BrendonBuilds/mod0/CAD/Extruders/E3DRevoHemeraXS_FLYRRF36_CAN/README.md

# E3DRevoHemeraXS_FLYRRF36_CAN_magZ-v1

- *This project is a work in progress*
- *Expect files to change*

## BOM

- Magnetic Connectors - https://www.adafruit.com/product/5360
- Limit Switch - https://www.digikey.com/en/products/detail/omron-electronics-inc-emc-div/D2GW-A02D/15963578

## Reference Models

- FLY RRF 36 Toolboards
  - https://teamgloomy.github.io/fly_rrf_36_general.html
- E3D Hemera XS:
  - https://e3d-online.com/products/revo-hemera-xs
  - https://cdn.shopify.com/s/files/1/0259/1948/8059/files/Hemera_XS_Reference_CAD.STEP?v=1693395523

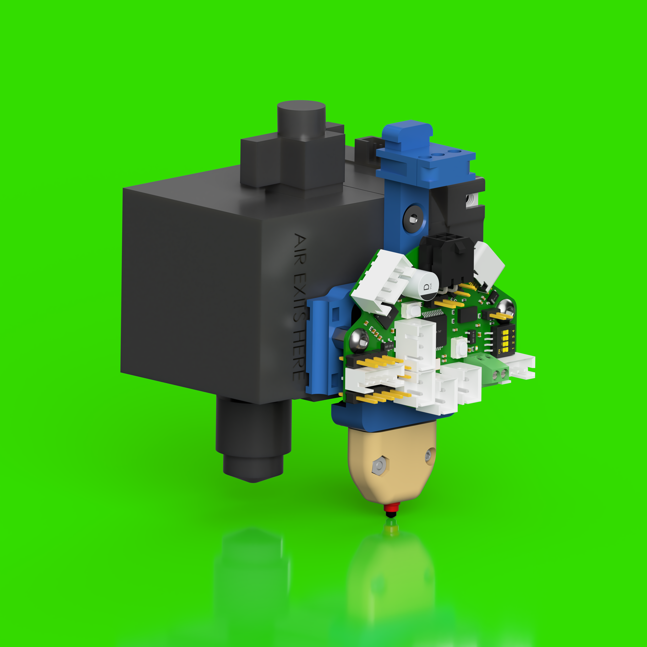
[picture p19: CAD/Extruders/E3DRevoHemeraXS_FLYRRF36_CAN/E3DRevoHemeraXS_FLYRRF36_CAN_magZ.PNG]
