BrendonBuilds/mod0/Art/mod0-github-link-qr.png

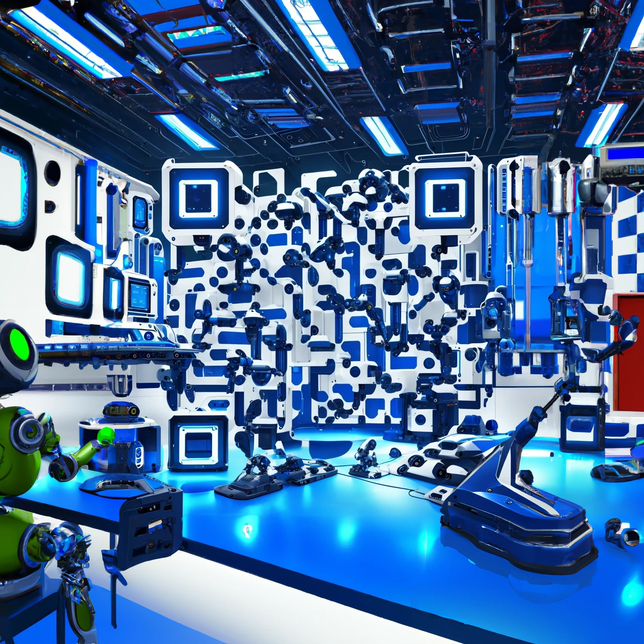
Art/mod0-github-link-qr.png
