BrendonBuilds/mod0/CAD/Bed-180/bed-support-bends-g30-galvanized-0.048in-v1.png

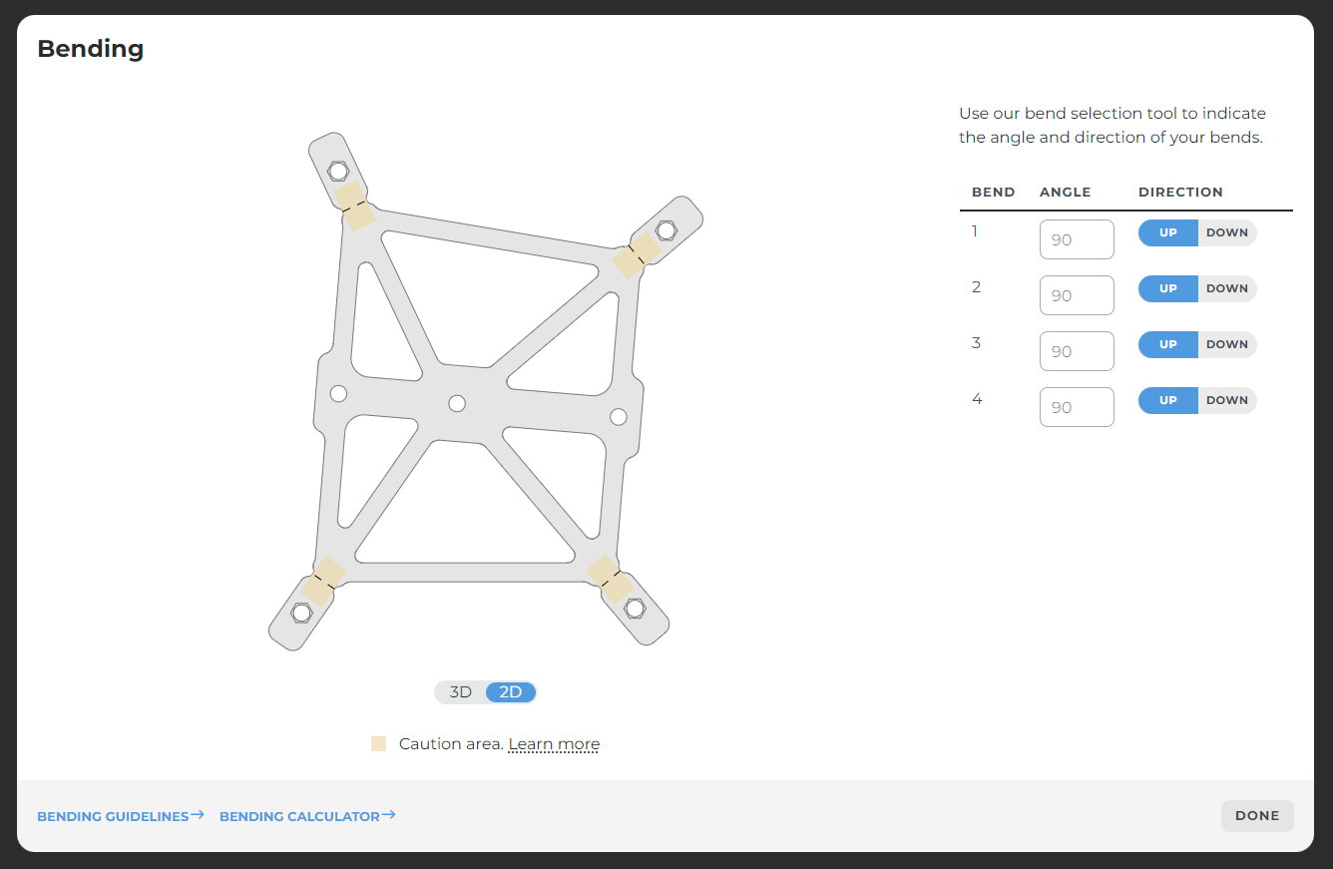
CAD/Bed-180/bed-support-bends-g30-galvanized-0.048in-v1.png
